karrika/Otaku-flash/pin_definitions.h

// Don't change the pin definitions.
// Optimizations expect that they are in these positions.

// Address pins.
#define A0 0
#define A1 1
#define A2 2
#define A3 3
#define A4 4
#define A5 5
#define A6 6
#define A7 7
#define A8 8
#define A9 9
#define A10 10
#define A11 11
#define A12 12
#define A13 13
#define A14 14
#define A15 26

// Control pins.
#define RW 25
#define HALT 27

// Data pins.
#define D0 15
#define D1 16
#define D2 17
#define D3 18
#define D4 19
#define D5 20
#define D6 21
#define D7 22
